syk-yaman/smart-led/Code/SmartLed/stdutils.h

/***************************************************************************************************
                                   ExploreEmbedded	
****************************************************************************************************
 * File:   stdutils.h
 * Version: 15.1
 * Author: ExploreEmbedded
 * Website: http://www.exploreembedded.com/wiki
 * Description: Contains standard util macros, typedefs and constants

The libraries have been tested on ExploreEmbedded development boards. We strongly believe that the 
library works on any of development boards for respective controllers. However, ExploreEmbedded 
disclaims any kind of hardware failure resulting out of usage of libraries, directly or indirectly.
Files may be subject to change without prior notice. The revision history contains the information 
related to updates. 


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
Errors and omissions should be reported to codelibraries@exploreembedded.com
 **************************************************************************************************/




/***************************************************************************************************
                             Revision History
****************************************************************************************************
15.0: Initial version 
15.1: Changed the prefix of bit masks from M_ to MASK_
      Added the section others macros
	  Defined the constants for Number system
***************************************************************************************************/



#ifndef _STD_UTIL_H_
#define	_STD_UTIL_H_


#ifndef F_CPU
#define F_CPU 16000000UL
#endif


/***************************************************************************************************
    Basic data types for 8051/PIC/AVR 8bit controllers
 ***************************************************************************************************/

/**----------char 8-bit--------
     char (-128 to 127)
     signed char (-128 to 127)
     unsigned char (0 - 255)
	-----------------------------*/

/**---------int 16-bit----------
	 int (-32768 to 32767)
	 signed int (-32768 to 32767)
     unsigned int (0 to 65535)
	 -----------------------------*/

typedef signed char     sint8_t;
typedef unsigned char   uint8_t;

typedef signed int      sint16_t;
typedef unsigned int    uint16_t;

typedef signed long int    sint32_t;
typedef unsigned long int  uint32_t;

#define C_SINT8_MAX   0x7F
#define C_SINT8_MIN  -128

#define C_UINT8_MAX   0xFFu
#define C_UINT8_MIN   0x00u

#define C_SINT16_MAX  32767
#define C_SINT16_MIN -32768

#define C_UINT16_MAX  0xFFFFu
#define C_UINT16_MIN  0x00u

#define C_SINT32_MAX  2147483647
#define C_SINT32_MIN -2147483648

#define C_UINT32_MAX  0xFFFFFFFFu
#define C_UINT32_MIN  0x00u
/***************************************************************************************************/



/***************************************************************************************************
                           Definition of common Bit-Masks
 ***************************************************************************************************/
#define  Mask_BIT0   0x0001u
#define  Mask_BIT1   0x0002u
#define  Mask_BIT2   0x0004u
#define  Mask_BIT3   0x0008u
#define  Mask_BIT4   0x0010u
#define  Mask_BIT5   0x0020u
#define  Mask_BIT6   0x0040u
#define  Mask_BIT7   0x0080u
#define  Mask_BIT8   0x0100u
#define  Mask_BIT9   0x0200u
#define  Mask_BIT10  0x0400u
#define  Mask_BIT11  0x0800u
#define  Mask_BIT12  0x1000u
#define  Mask_BIT13  0x2000u
#define  Mask_BIT14  0x4000u
#define  Mask_BIT15  0x8000u
/**************************************************************************************************/





/***************************************************************************************************
                           Port Direction configurations
 ***************************************************************************************************/
#define C_PinOutput_U8     0x01u
#define C_PinInput_U8      0x00u
#define C_PortOutput_U8    0xFFu
#define C_PortInput_U8     0x00u

#define INPUT              C_PinInput_U8
#define OUTPUT             C_PinOutput_U8
#define LOW                0x00u
#define HIGH               0x01u
/**************************************************************************************************/






/***************************************************************************************************
                              Commonly used constants
 **************************************************************************************************/
#define C_ZERO_U8          0x00u
#define C_NULL_U8          0x00u
#define NULL_CHAR          0x00u


#define FALSE              0x00u
#define TRUE               0x01u

#define C_NOTOK_U8         0x00u
#define C_OK_U8            0x01u

#define C_INVALID_U8       0x00u
#define C_VALID_U8         0x01u

#define C_FAILED_U8        0x00u
#define C_SUCCESSFUL_U8    0x01u
#define C_BUSY_U8          0x02u


#define C_BINARY_U8           2u
#define C_DECIMAL_U8         10u
#define C_HEX_U8             16u
/**************************************************************************************************/






/***************************************************************************************************
                                Standard Enumerations and Constants
***************************************************************************************************/
typedef enum
{
   E_FALSE,
   E_TRUE   
}Boolean_et;


typedef enum
{
    E_FAILED,
    E_SUCCESS,
    E_BUSY,
    E_TIMEOUT
}Status_et;


typedef enum
{
	E_BINARY=2,
	E_DECIMAL = 10,
	E_HEX = 16
}NumericSystem_et;
/**************************************************************************************************/ 







/***************************************************************************************************
                                Macros for Bit Manipulation
 ****************************************************************************************************/
#define  util_GetBitMask(bit)          (1<<(bit))
#define  util_BitSet(x,bit)            ((x) |=  util_GetBitMask(bit))
#define  util_BitClear(x,bit)          ((x) &= ~util_GetBitMask(bit))
#define  util_BitToggle(x,bit)         ((x) ^=  util_GetBitMask(bit))
#define  util_UpdateBit(x,bit,val)     ((val)? util_BitSet(x,bit): util_BitClear(x,bit))


#define  util_GetBitStatus(x,bit)      (((x)&(util_GetBitMask(bit)))!=0u)
#define  util_IsBitSet(x,bit)          (((x)&(util_GetBitMask(bit)))!=0u)
#define  util_IsBitCleared(x,bit)      (((x)&(util_GetBitMask(bit)))==0u)


#define  util_AreAllBitsSet(x,BitMask) (((x)&(BitMask))==BitMask)
#define  util_AreAnyBitsSet(x,BitMask) (((x)&(BitMask))!=0x00u)
/**************************************************************************************************/





/***************************************************************************************************
                             Macros to find the mod of a number
 ***************************************************************************************************/
#define util_GetMod8(dividend,divisor)  (uint8_t) (dividend - (divisor * (uint8_t) (dividend/divisor)))
#define util_GetMod16(dividend,divisor) (uint16_t)(dividend - (divisor * (uint16_t)(dividend/divisor)))
#define util_GetMod32(dividend,divisor) (uint32_t)(dividend - (divisor * (uint32_t)(dividend/divisor)))
/***************************************************************************************************/





/***************************************************************************************************
                          Macros for Dec2Ascii,Hec2Ascii and Acsii2Hex conversion
 ****************************************************************************************************/
#define util_Dec2Ascii(Dec)	 ((Dec)+0x30)
#define util_Ascii2Dec(Asc)	 ((Asc)-0x30)
#define util_Hex2Ascii(Hex)  (((Hex)>0x09) ? ((Hex) + 0x37): ((Hex) + 0x30)) 
#define util_Ascii2Hex(Asc)  (((Asc)>0x39) ? ((Asc) - 0x37): ((Asc) - 0x30))
/***************************************************************************************************/





/***************************************************************************************************
                     Macros to extract the nibbles
 ***************************************************************************************************/
#define util_ExtractNibble0to4(x)    (uint8_t) ((x) & 0x0Fu)
#define util_ExtractNibble4to8(x)    (uint8_t) (((x)>>4)  & 0x0Fu)
#define util_ExtractNibble8to12(x)   (uint8_t) (((x)>>8)  & 0x0Fu)
#define util_ExtractNibble12to16(x)  (uint8_t) (((x)>>12) & 0x0Fu)
/**************************************************************************************************/






/***************************************************************************************************
                     Macros to extract the Byte
***************************************************************************************************/
#define util_ExtractByte0to8(x)    (uint8_t) ((x) & 0xFFu)
#define util_ExtractByte8to16(x)   (uint8_t) (((x)>>8) & 0xFFu)
#define util_ExtractByte16to28(x)  (uint8_t) (((x)>>16) & 0xFFu)
#define util_ExtractByte28to32(x)  (uint8_t) (((x)>>28) & 0xFFu)
/**************************************************************************************************/






/***************************************************************************************************
                      Other Macros
***************************************************************************************************/
#define util_GetMax(num1,num2)     (((num1)>(num2))? (num1): (num2)) 
#define util_GetMin(num1,num2)     (((num1)<(num2))? (num1): (num2)) 

#define util_swap(x,y)             (x ^= y ^= x ^= y)
#define util_GetAbsolute(x)	       (((x) < 0) ? -(x) : (x))
/**************************************************************************************************/







#endif	
